pondersson/ack42/cad/util/bezier_curve.scad

/**
 * bezier_curve.scad
 *
 * @copyright Justin Lin, 2017
 * @license https://opensource.org/licenses/lgpl-3.0.html
 *
 * @see https://openhome.cc/eGossip/OpenSCAD/lib2x-bezier_curve.html
 *
 **/

function __to2d(p) = [p[0], p[1]];

function _combi(n, k) =
  let(
    bi_coef = [
      [1],     // n = 0: for padding
      [1,1],    // n = 1: for Linear curves, how about drawing a line directly?
      [1,2,1],   // n = 2: for Quadratic curves
      [1,3,3,1]   // n = 3: for Cubic Bézier curves
      ]
    )
  n < len(bi_coef) ? bi_coef[n][k] : (
    k == 0 ? 1 : (_combi(n, k - 1) * (n - k + 1) / k)
    );

function bezier_curve_coordinate(t, pn, n, i = 0) =
  i == n + 1 ? 0 :
  (_combi(n, i) * pn[i] * pow(1 - t, n - i) * pow(t, i) +
   bezier_curve_coordinate(t, pn, n, i + 1));

function _bezier_curve_point(t, points) =
  let(n = len(points) - 1)
  [
    bezier_curve_coordinate(
      t,
      [for(p = points) p[0]],
      n
      ),
    bezier_curve_coordinate(
      t,
      [for(p = points) p[1]],
      n
      ),
    bezier_curve_coordinate(
      t,
      [for(p = points) p[2]],
      n
      )
    ];

function bezier_curve(t_step, points) =
  let(
    t_end = ceil(1 / t_step),
    pts = concat([
                   for(t = 0; t < t_end; t = t + 1)
                     _bezier_curve_point(t * t_step, points)
                   ], [_bezier_curve_point(1, points)])
    )
  len(points[0]) == 3 ? pts : [for(pt = pts) __to2d(pt)];
